jasiek/ESP8266-PowerMonitor/pictures/PIR_assembled2.jpg

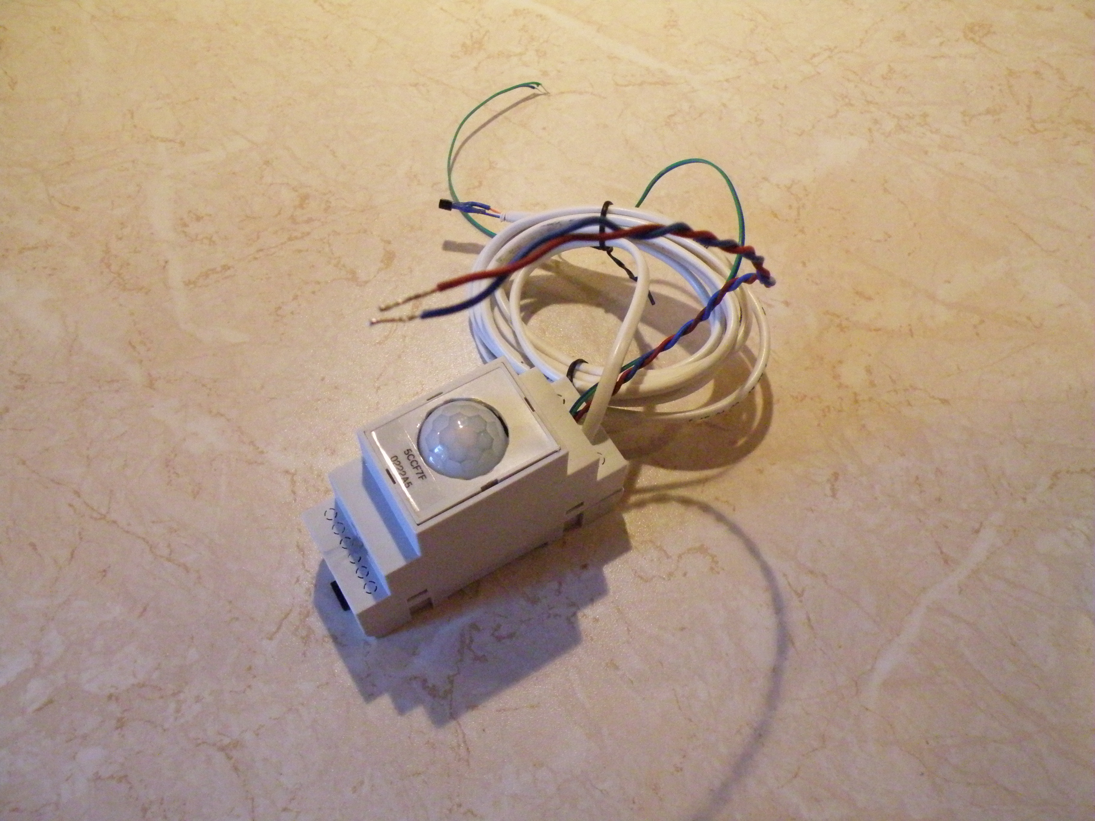
pictures/PIR_assembled2.jpg
