jasiek/ESP8266-PowerMonitor/pictures/PIR_installed.jpg

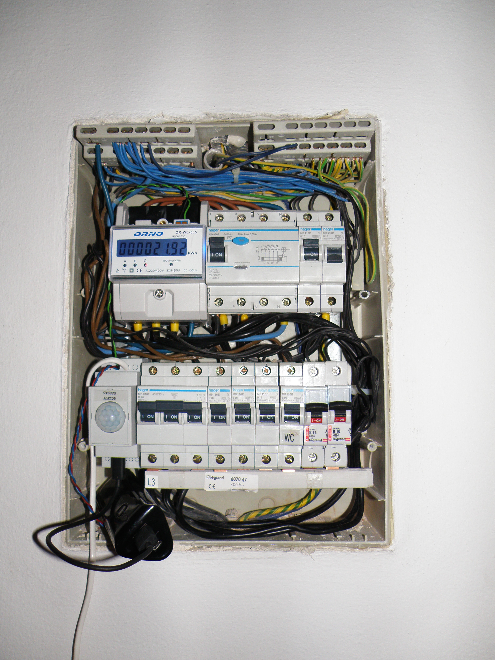
pictures/PIR_installed.jpg
